zatullier/Magnetic-Analysis/fixture/drawings/P05A.dxf

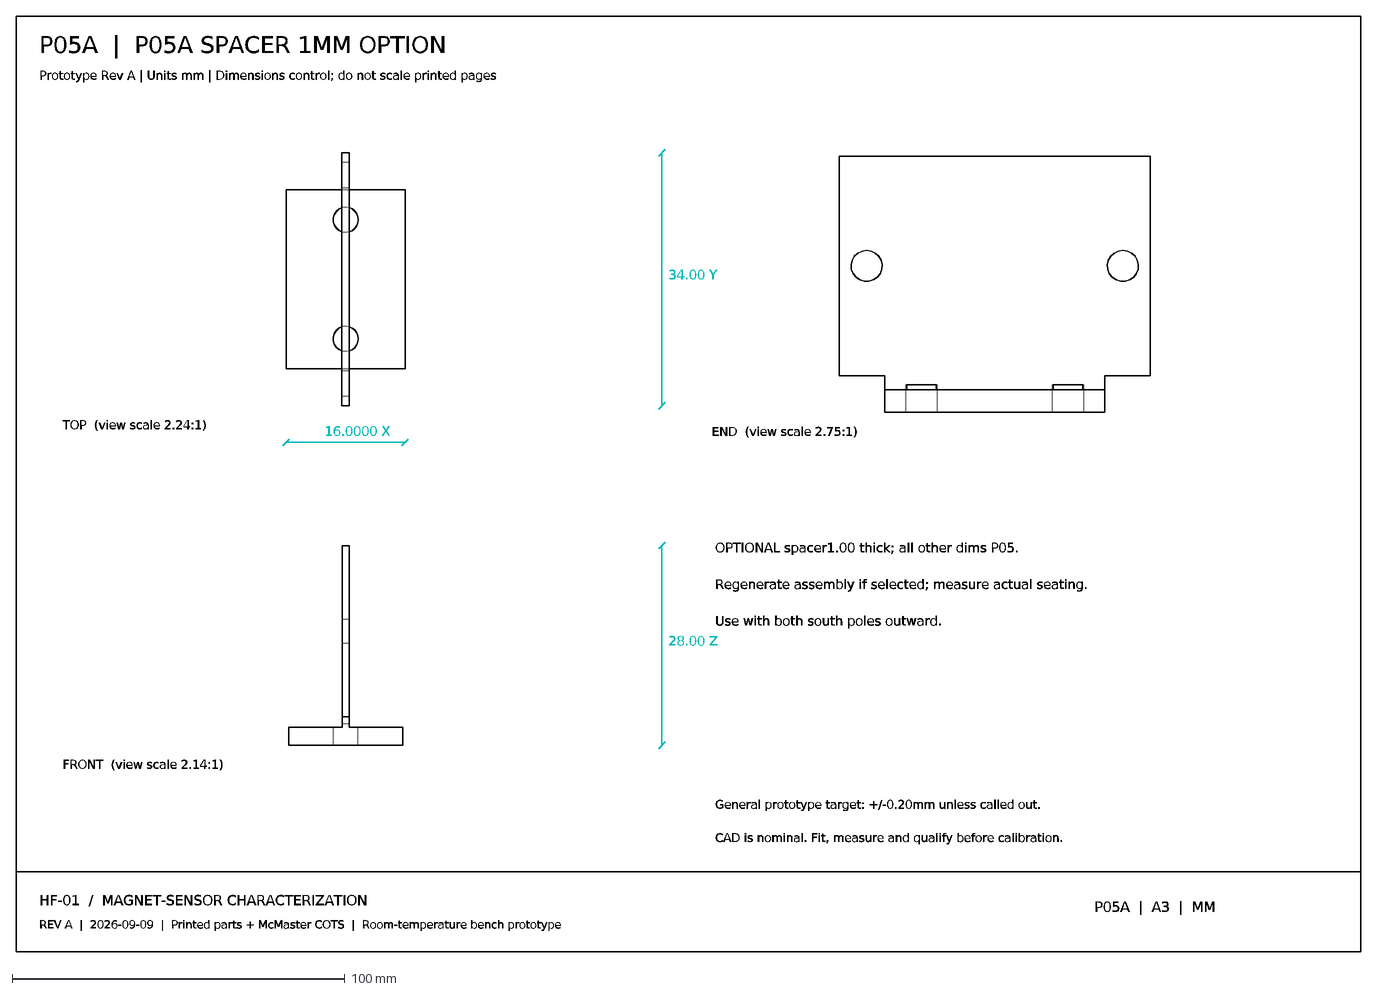
[picture p29: CAD file, 2026-09-19]
fixture/drawings/P05A.dxf
P05A | P05A SPACER 1MM OPTION
Prototype Rev A | Units mm | Dimensions control; do not scale printed pages
HF-01 / MAGNET-SENSOR CHARACTERIZATION
REV A | 2026-09-09 | Printed parts + McMaster COTS | Room-temperature bench prototype
P05A | A3 | MM
TOP (view scale 2.24:1)
FRONT (view scale 2.14:1)
END (view scale 2.75:1)
16.0000 X
34.00 Y
28.00 Z
OPTIONAL spacer1.00 thick; all other dims P05.
Regenerate assembly if selected; measure actual seating.
Use with both south poles outward.
General prototype target: +/-0.20mm unless called out.
CAD is nominal. Fit, measure and qualify before calibration.
