zatullier/Magnetic-Analysis/fixture/step/P03_keeper_qty2.step

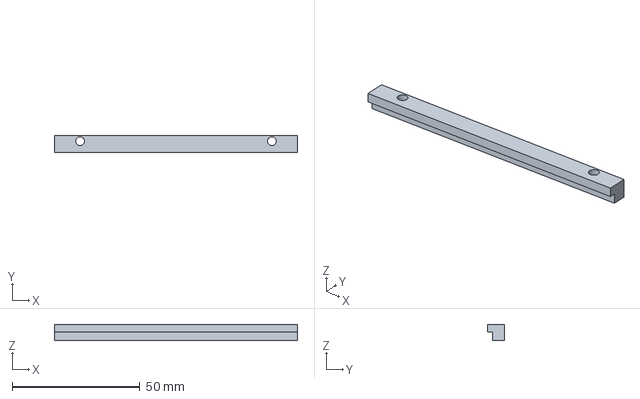
[picture p30: CAD file, 2026-09-19]
fixture/step/P03_keeper_qty2.step
95.0 x 6.80 x 6.30 mm
