zatullier/Magnetic-Analysis/fixture/drawings/P07.dxf

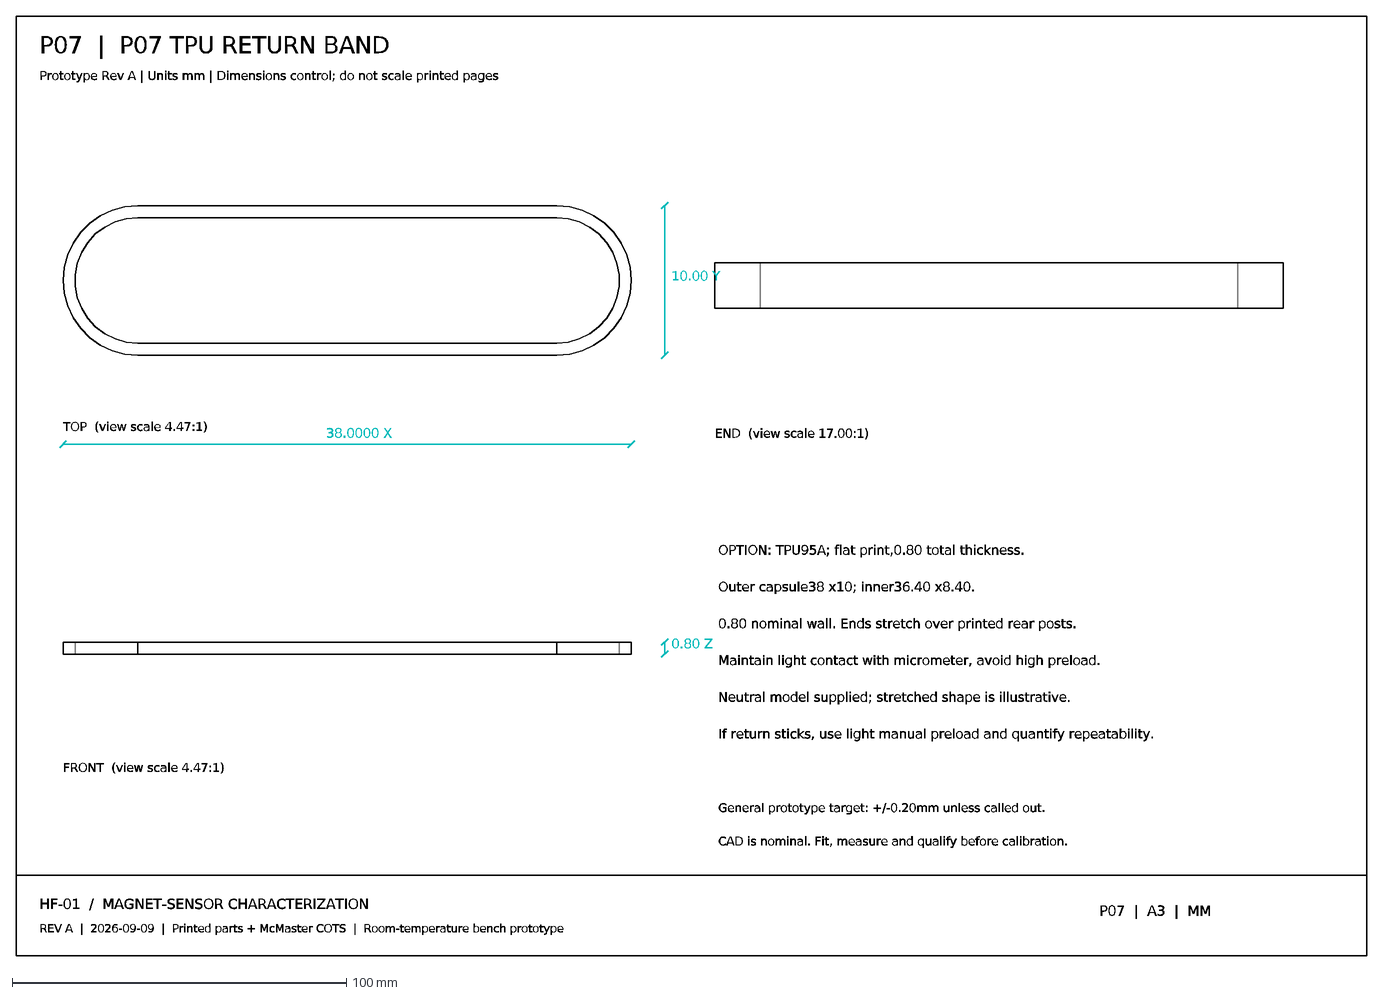
[picture p31: CAD file, 2026-09-19]
fixture/drawings/P07.dxf
P07 | P07 TPU RETURN BAND
Prototype Rev A | Units mm | Dimensions control; do not scale printed pages
HF-01 / MAGNET-SENSOR CHARACTERIZATION
REV A | 2026-09-09 | Printed parts + McMaster COTS | Room-temperature bench prototype
P07 | A3 | MM
TOP (view scale 4.47:1)
FRONT (view scale 4.47:1)
END (view scale 17.00:1)
38.0000 X
10.00 Y
0.80 Z
OPTION: TPU95A; flat print,0.80 total thickness.
Outer capsule38 x10; inner36.40 x8.40.
0.80 nominal wall. Ends stretch over printed rear posts.
Maintain light contact with micrometer, avoid high preload.
Neutral model supplied; stretched shape is illustrative.
If return sticks, use light manual preload and quantify repeatability.
General prototype target: +/-0.20mm unless called out.
CAD is nominal. Fit, measure and qualify before calibration.
