zatullier/Magnetic-Analysis/fixture/step/P09_table_foot_qty4.step

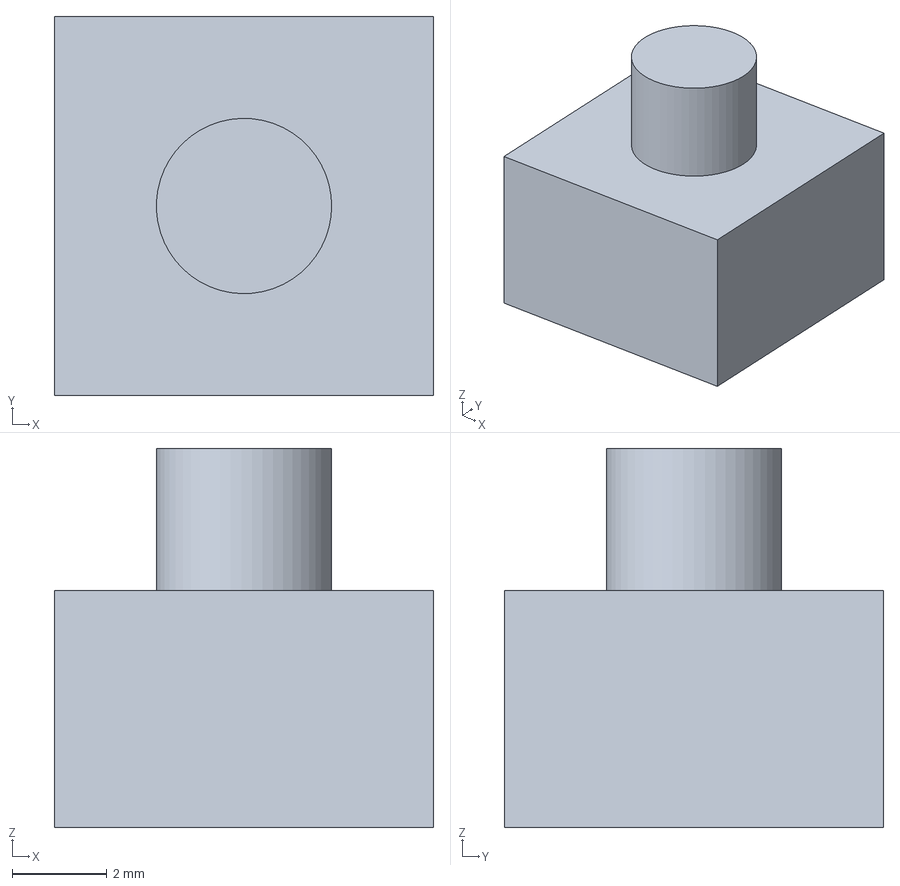
[picture p32: CAD file, 2026-09-19]
fixture/step/P09_table_foot_qty4.step
8.00 x 8.00 x 8.00 mm
