zatullier/Magnetic-Analysis/fixture/drawings/P06.dxf

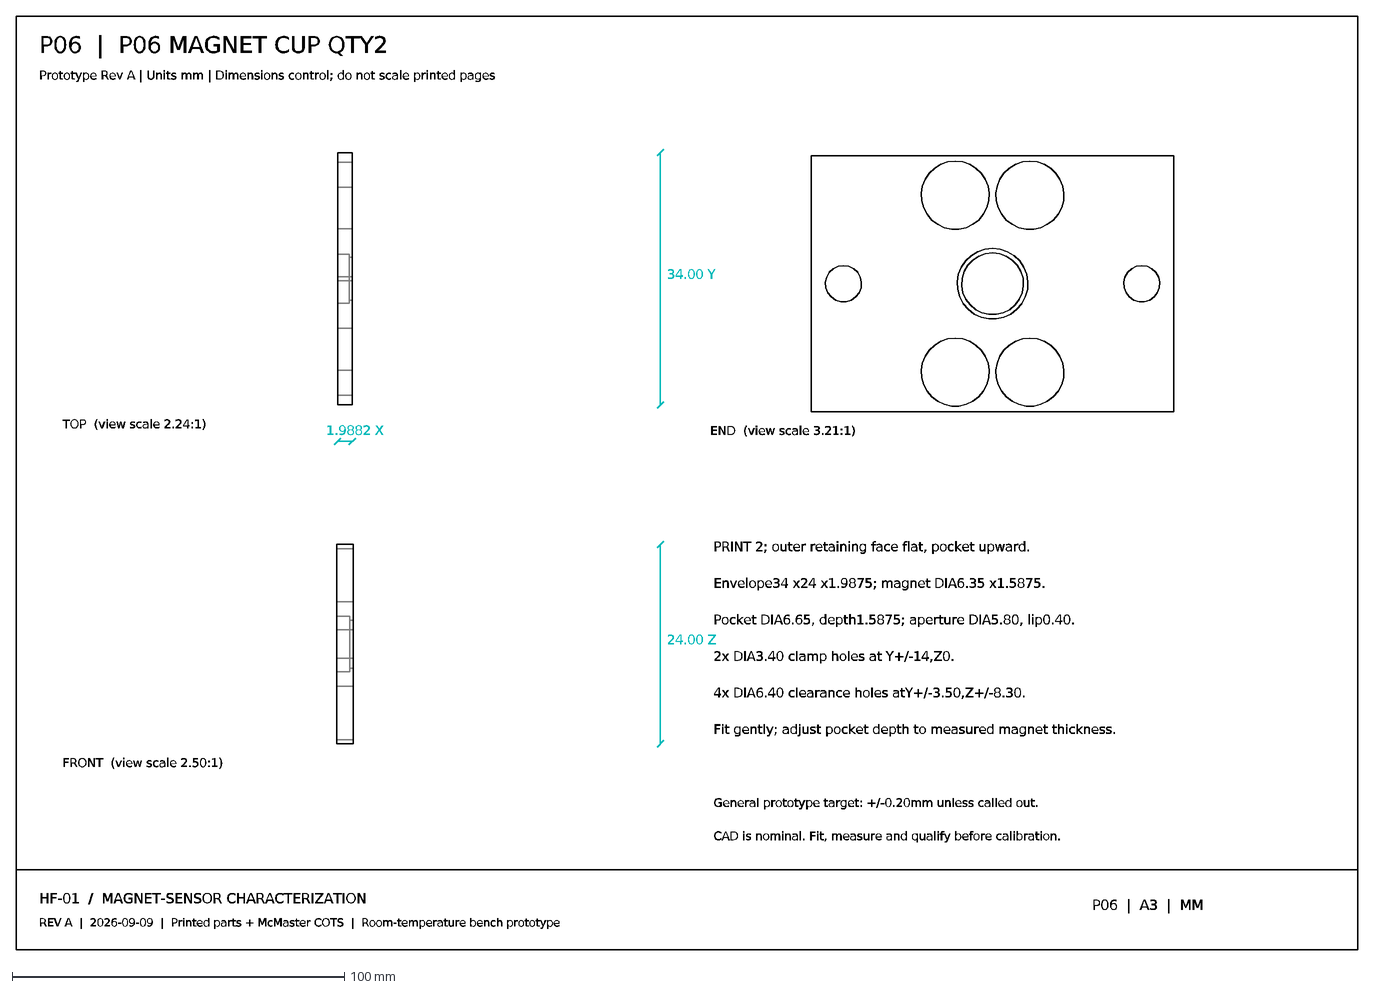
[picture p33: CAD file, 2026-09-19]
fixture/drawings/P06.dxf
P06 | P06 MAGNET CUP QTY2
Prototype Rev A | Units mm | Dimensions control; do not scale printed pages
HF-01 / MAGNET-SENSOR CHARACTERIZATION
REV A | 2026-09-09 | Printed parts + McMaster COTS | Room-temperature bench prototype
P06 | A3 | MM
TOP (view scale 2.24:1)
FRONT (view scale 2.50:1)
END (view scale 3.21:1)
1.9882 X
34.00 Y
24.00 Z
PRINT 2; outer retaining face flat, pocket upward.
Envelope34 x24 x1.9875; magnet DIA6.35 x1.5875.
Pocket DIA6.65, depth1.5875; aperture DIA5.80, lip0.40.
2x DIA3.40 clamp holes at Y+/-14,Z0.
4x DIA6.40 clearance holes atY+/-3.50,Z+/-8.30.
Fit gently; adjust pocket depth to measured magnet thickness.
General prototype target: +/-0.20mm unless called out.
CAD is nominal. Fit, measure and qualify before calibration.
