zatullier/Magnetic-Analysis/fixture/step/P05_spacer_3mm.step

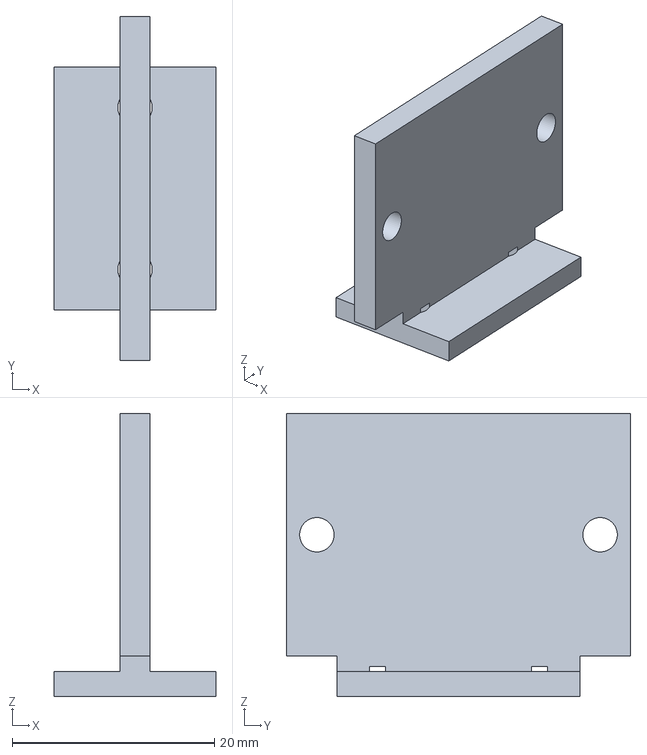
[picture p34: CAD file, 2026-09-19]
fixture/step/P05_spacer_3mm.step
16.0 x 34.0 x 28.0 mm
