zatullier/Magnetic-Analysis/fixture/drawings/P05B.dxf

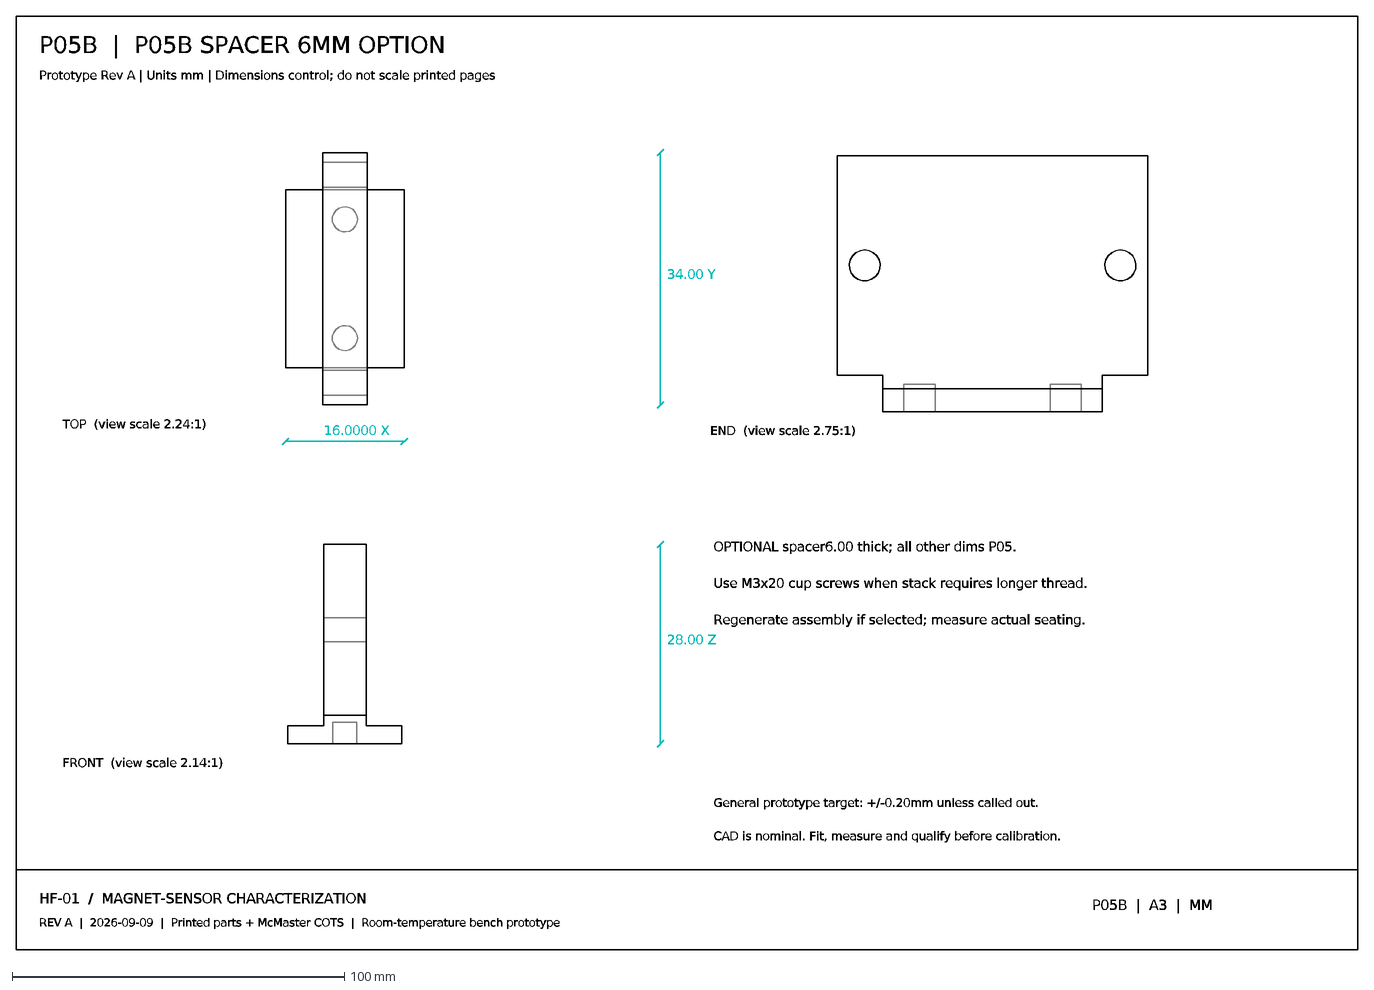
[picture p35: CAD file, 2026-09-19]
fixture/drawings/P05B.dxf
P05B | P05B SPACER 6MM OPTION
Prototype Rev A | Units mm | Dimensions control; do not scale printed pages
HF-01 / MAGNET-SENSOR CHARACTERIZATION
REV A | 2026-09-09 | Printed parts + McMaster COTS | Room-temperature bench prototype
P05B | A3 | MM
TOP (view scale 2.24:1)
FRONT (view scale 2.14:1)
END (view scale 2.75:1)
16.0000 X
34.00 Y
28.00 Z
OPTIONAL spacer6.00 thick; all other dims P05.
Use M3x20 cup screws when stack requires longer thread.
Regenerate assembly if selected; measure actual seating.
General prototype target: +/-0.20mm unless called out.
CAD is nominal. Fit, measure and qualify before calibration.
