zatullier/Magnetic-Analysis/fixture/step/P05A_spacer_1mm_OPTION.step

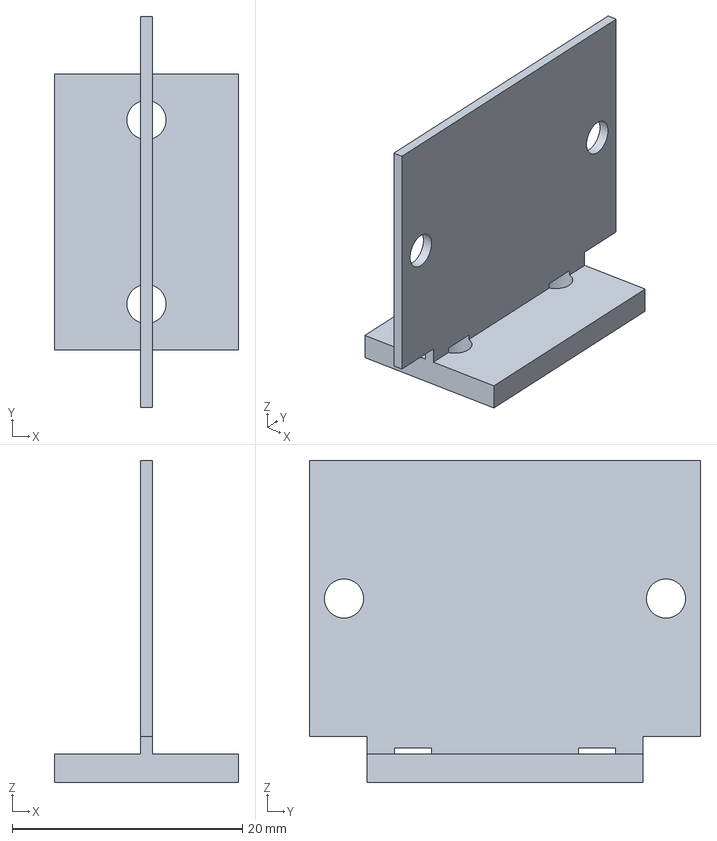
[picture p36: CAD file, 2026-09-19]
fixture/step/P05A_spacer_1mm_OPTION.step
16.0 x 34.0 x 28.0 mm
