zatullier/Magnetic-Analysis/fixture/drawings/P04.dxf

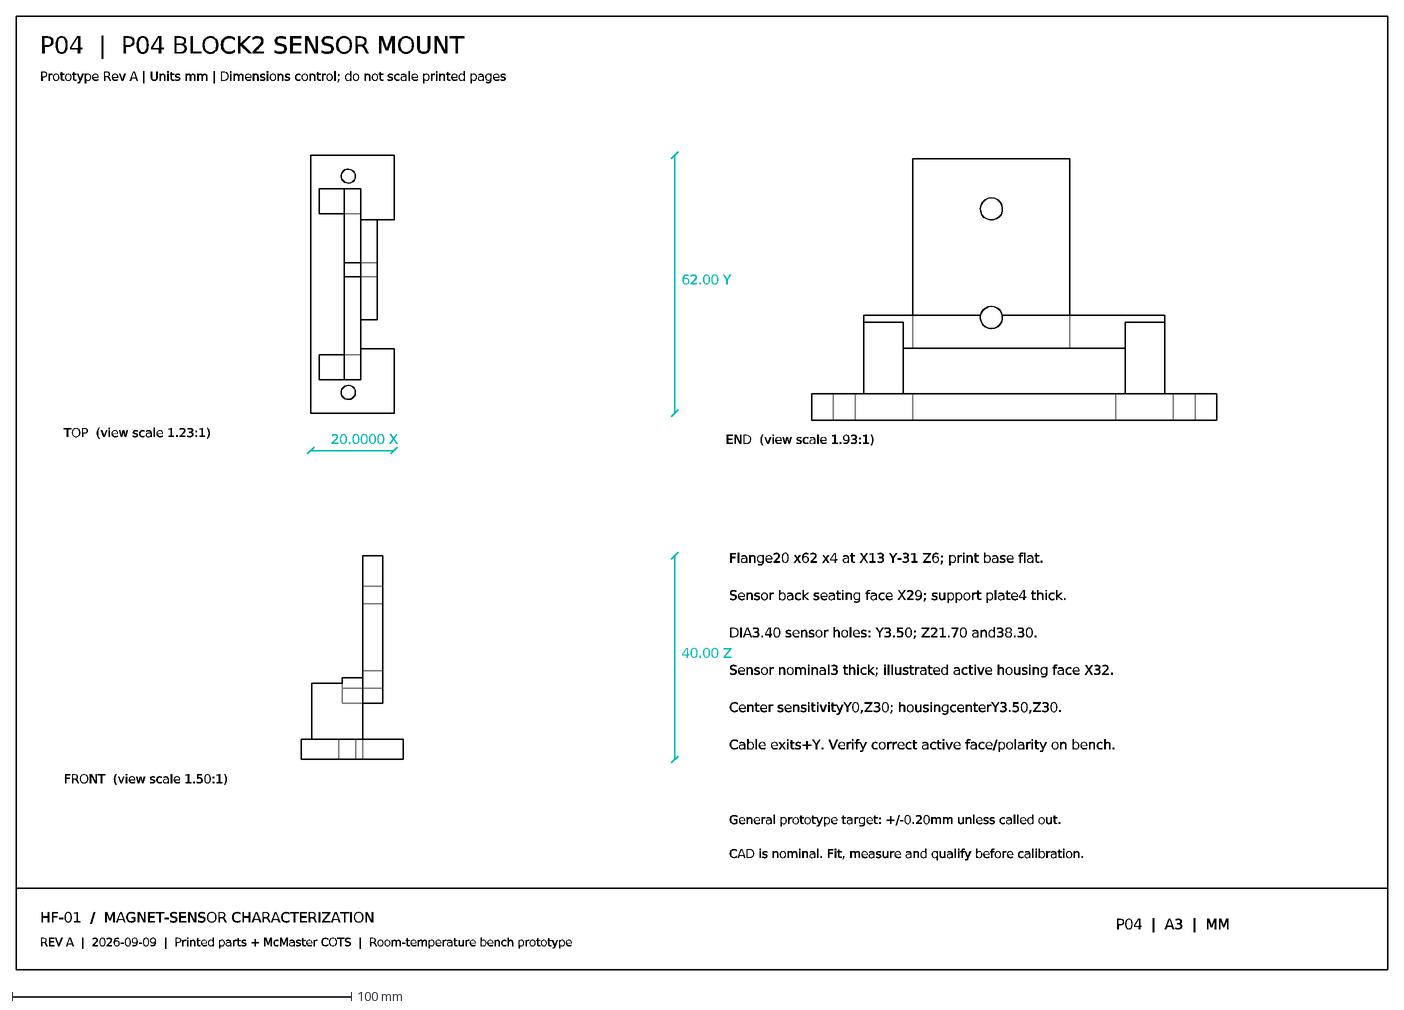
[picture p37: CAD file, 2026-09-19]
fixture/drawings/P04.dxf
P04 | P04 BLOCK2 SENSOR MOUNT
Prototype Rev A | Units mm | Dimensions control; do not scale printed pages
HF-01 / MAGNET-SENSOR CHARACTERIZATION
REV A | 2026-09-09 | Printed parts + McMaster COTS | Room-temperature bench prototype
P04 | A3 | MM
TOP (view scale 1.23:1)
FRONT (view scale 1.50:1)
END (view scale 1.93:1)
20.0000 X
62.00 Y
40.00 Z
Flange20 x62 x4 at X13 Y-31 Z6; print base flat.
Sensor back seating face X29; support plate4 thick.
DIA3.40 sensor holes: Y3.50; Z21.70 and38.30.
Sensor nominal3 thick; illustrated active housing face X32.
Center sensitivityY0,Z30; housingcenterY3.50,Z30.
Cable exits+Y. Verify correct active face/polarity on bench.
General prototype target: +/-0.20mm unless called out.
CAD is nominal. Fit, measure and qualify before calibration.
