zatullier/Magnetic-Analysis/fixture/step/P08_5mm_reference_gauge.step

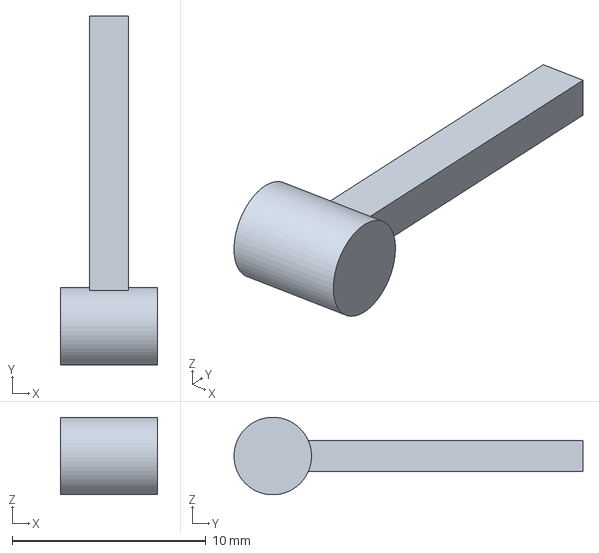
[picture p38: CAD file, 2026-09-19]
fixture/step/P08_5mm_reference_gauge.step
5.00 x 18.0 x 4.00 mm
