zatullier/Magnetic-Analysis/fixture/drawings/P09.dxf

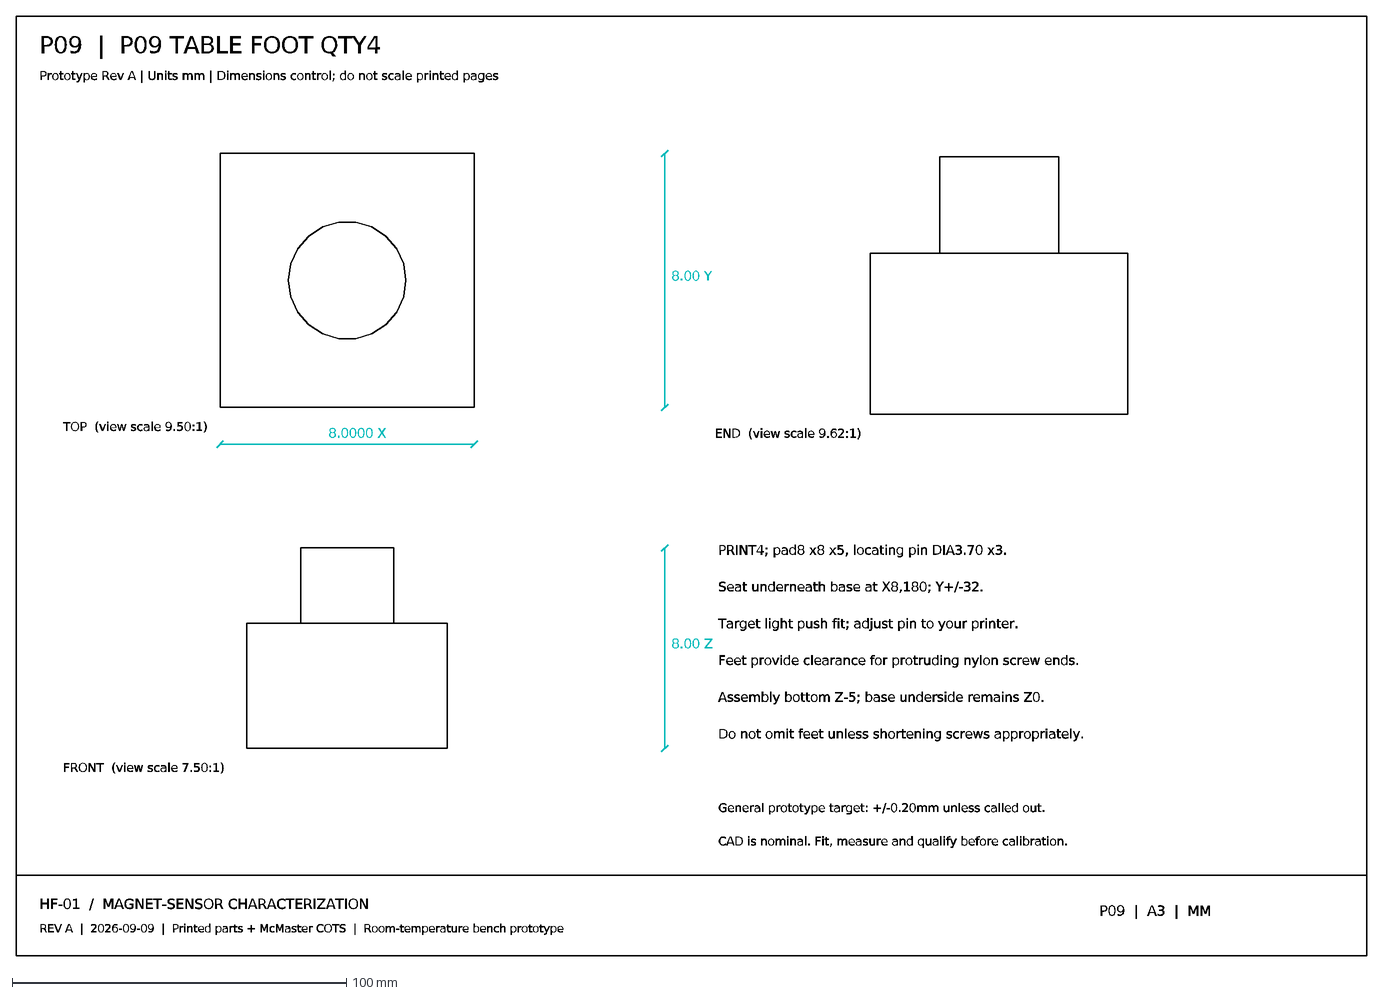
[picture p39: CAD file, 2026-09-19]
fixture/drawings/P09.dxf
P09 | P09 TABLE FOOT QTY4
Prototype Rev A | Units mm | Dimensions control; do not scale printed pages
HF-01 / MAGNET-SENSOR CHARACTERIZATION
REV A | 2026-09-09 | Printed parts + McMaster COTS | Room-temperature bench prototype
P09 | A3 | MM
TOP (view scale 9.50:1)
FRONT (view scale 7.50:1)
END (view scale 9.62:1)
8.0000 X
8.00 Y
8.00 Z
PRINT4; pad8 x8 x5, locating pin DIA3.70 x3.
Seat underneath base at X8,180; Y+/-32.
Target light push fit; adjust pin to your printer.
Feet provide clearance for protruding nylon screw ends.
Assembly bottom Z-5; base underside remains Z0.
Do not omit feet unless shortening screws appropriately.
General prototype target: +/-0.20mm unless called out.
CAD is nominal. Fit, measure and qualify before calibration.
