zatullier/Magnetic-Analysis/fixture/step/P01_base.step

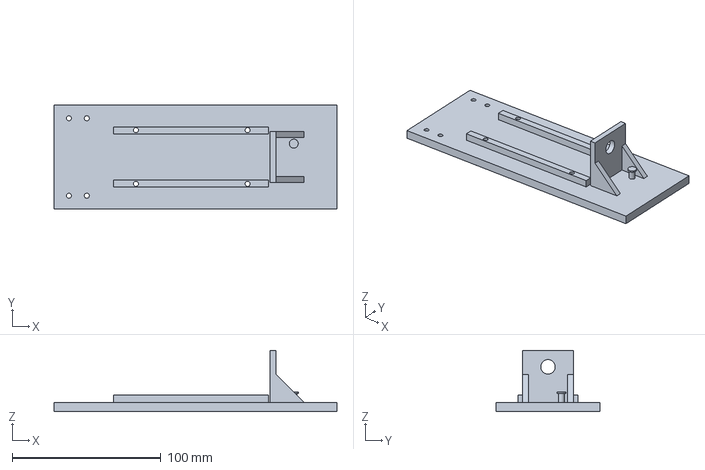
[picture p40: CAD file, 2026-09-19]
fixture/step/P01_base.step
190.0 x 70.0 x 41.0 mm
