zatullier/Magnetic-Analysis/fixture/drawings/P02.dxf

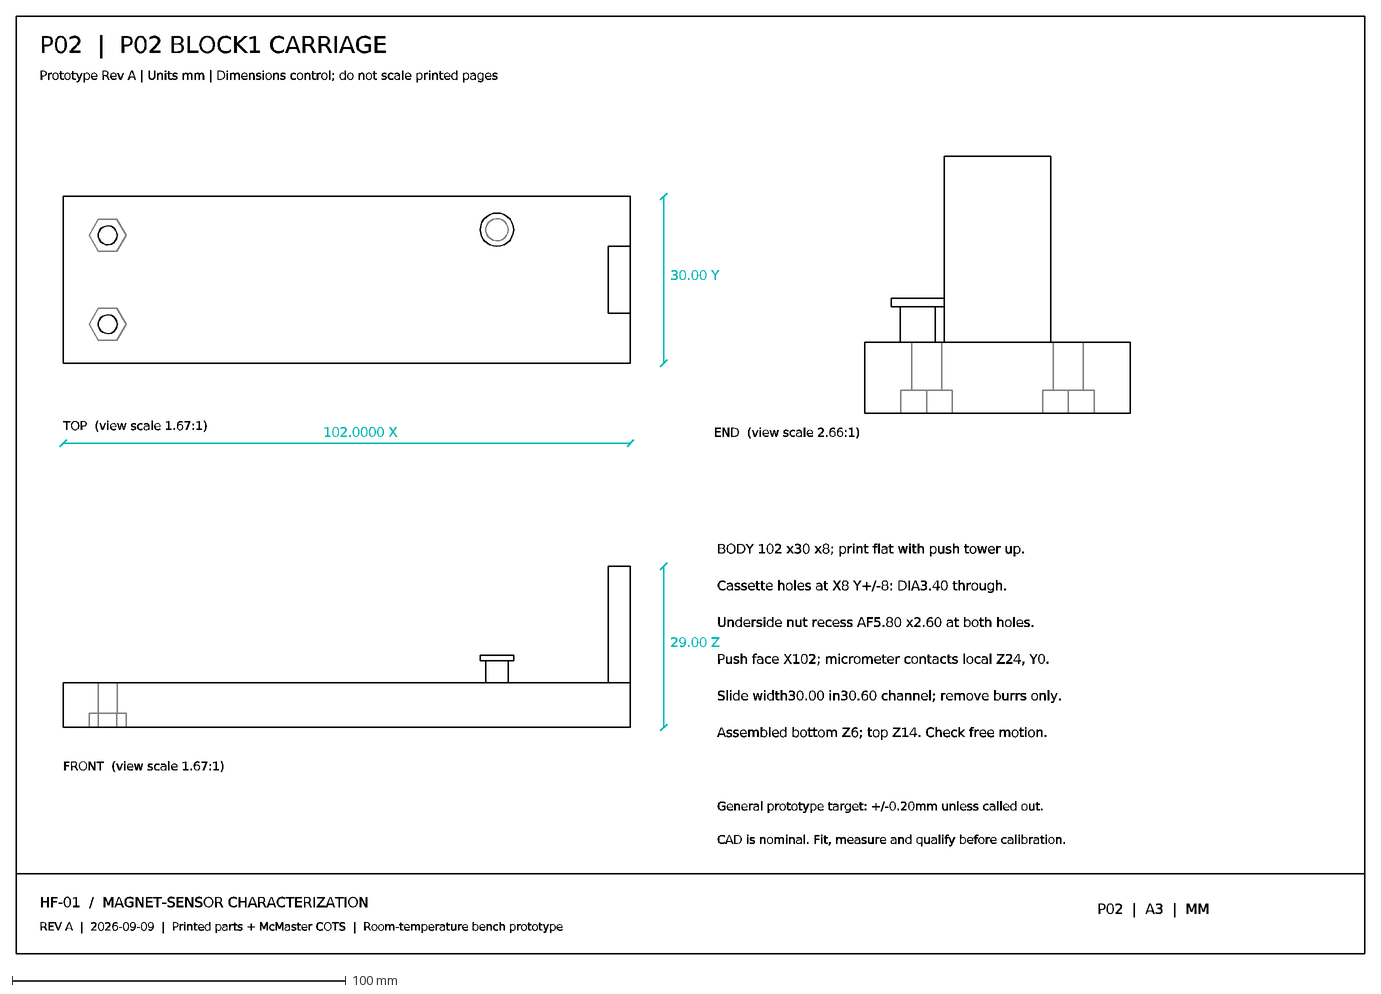
[picture p41: CAD file, 2026-09-19]
fixture/drawings/P02.dxf
P02 | P02 BLOCK1 CARRIAGE
Prototype Rev A | Units mm | Dimensions control; do not scale printed pages
HF-01 / MAGNET-SENSOR CHARACTERIZATION
REV A | 2026-09-09 | Printed parts + McMaster COTS | Room-temperature bench prototype
P02 | A3 | MM
TOP (view scale 1.67:1)
FRONT (view scale 1.67:1)
END (view scale 2.66:1)
102.0000 X
30.00 Y
29.00 Z
BODY 102 x30 x8; print flat with push tower up.
Cassette holes at X8 Y+/-8: DIA3.40 through.
Underside nut recess AF5.80 x2.60 at both holes.
Push face X102; micrometer contacts local Z24, Y0.
Slide width30.00 in30.60 channel; remove burrs only.
Assembled bottom Z6; top Z14. Check free motion.
General prototype target: +/-0.20mm unless called out.
CAD is nominal. Fit, measure and qualify before calibration.
